jphacks/TK_1621/Fusion360/bin/data/STL_RELEASE/RIGHT_LEG_R.stl

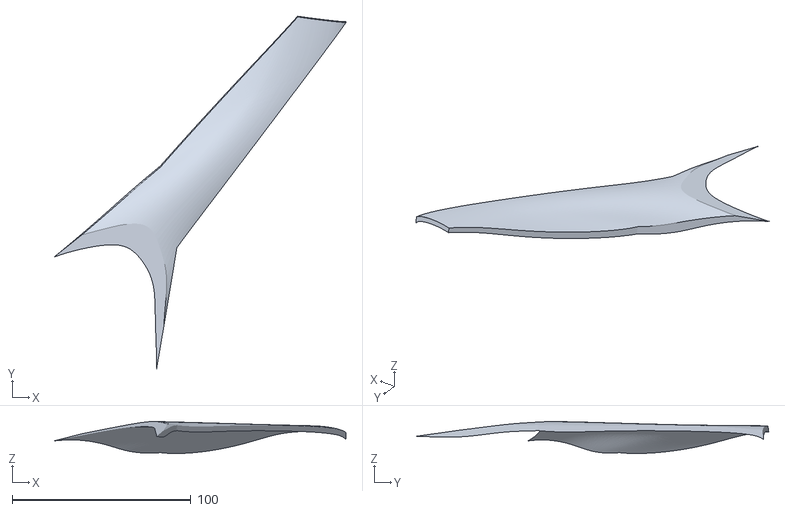
[picture p32: CAD file, 2016-11-25]
Fusion360/bin/data/STL_RELEASE/RIGHT_LEG_R.stl
163.2 x 197.1 x 17.9
