jphacks/TK_1621/Fusion360/bin/data/STL_MATERIAL/MOBILEBATTERY.stl

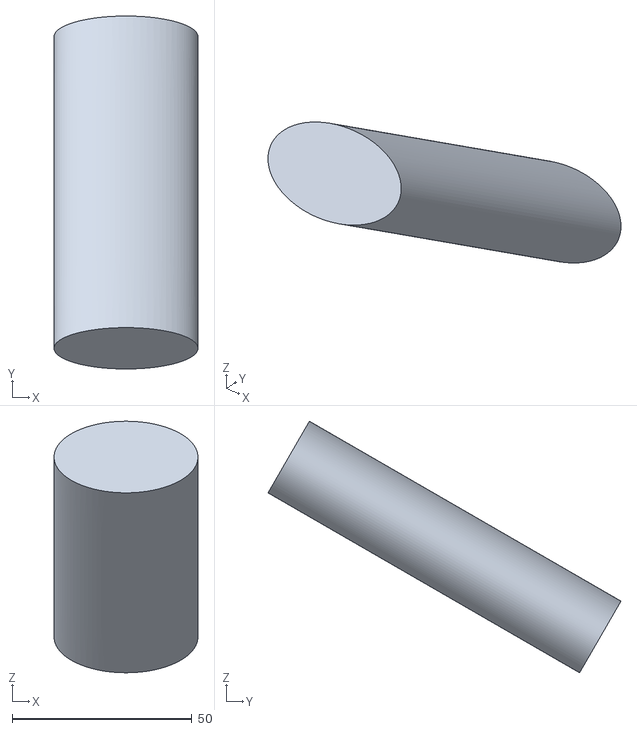
[picture p33: CAD file, 2016-10-29]
Fusion360/bin/data/STL_MATERIAL/MOBILEBATTERY.stl
40.0 x 98.1 x 69.9
