jphacks/TK_1621/Fusion360/bin/data/STL_RELEASE/LEFT_WING_R.stl

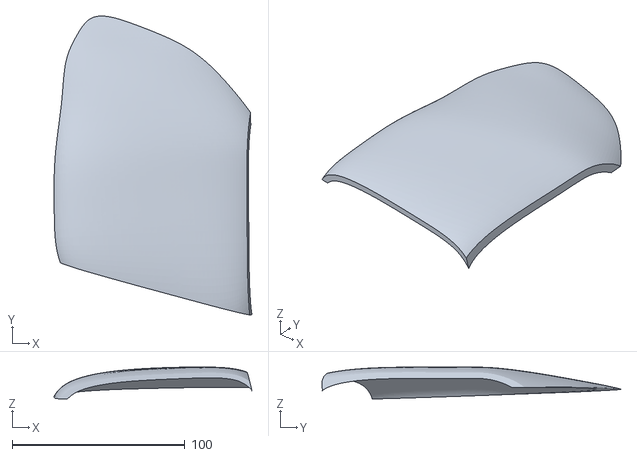
[picture p34: CAD file, 2016-11-25]
Fusion360/bin/data/STL_RELEASE/LEFT_WING_R.stl
114.6 x 173.1 x 18.5
