jphacks/TK_1621/Fusion360/bin/data/OF/RIGHT_LEG.stl

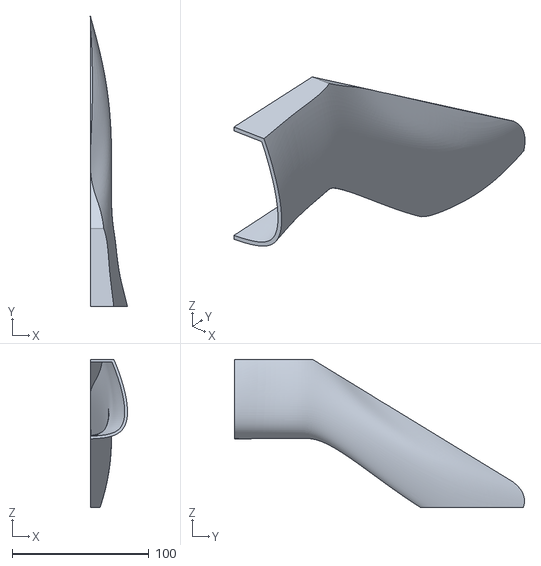
[picture p35: CAD file, 2016-10-30]
Fusion360/bin/data/OF/RIGHT_LEG.stl
27.1 x 211.7 x 108.3
