jphacks/TK_1621/Fusion360/bin/data/STL_RELEASE/BACK_RASP_R.stl

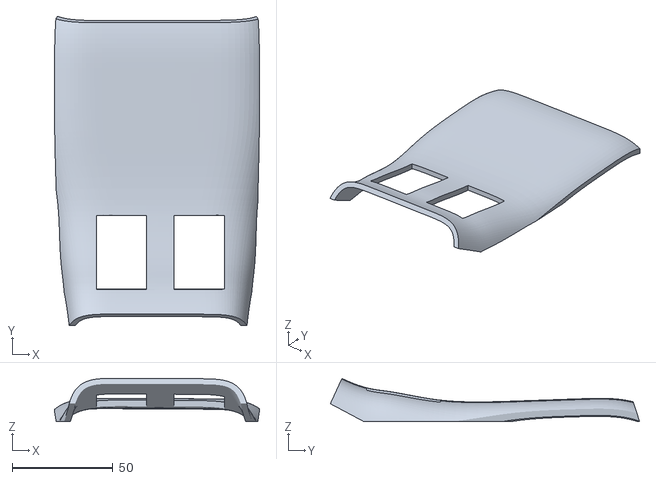
[picture p36: CAD file, 2016-11-25]
Fusion360/bin/data/STL_RELEASE/BACK_RASP_R.stl
101.9 x 153.7 x 21.5
