jphacks/TK_1621/Fusion360/bin/data/STL_RELEASE/FRONT_CAMERA_R.stl

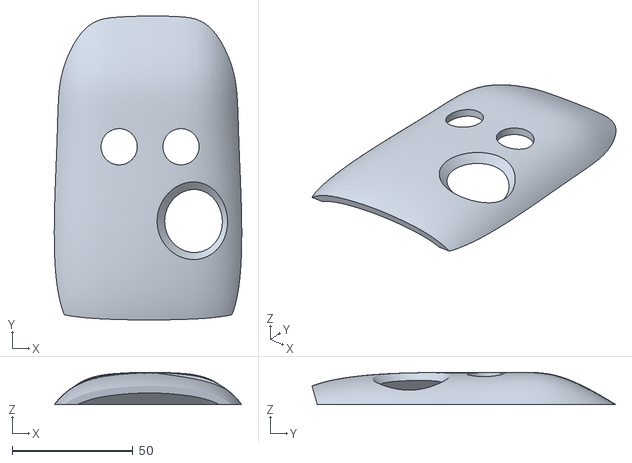
[picture p37: CAD file, 2016-11-25]
Fusion360/bin/data/STL_RELEASE/FRONT_CAMERA_R.stl
77.7 x 125.9 x 13.4
