jphacks/TK_1621/Fusion360/bin/data/STL_MATERIAL/WEBCAM.stl

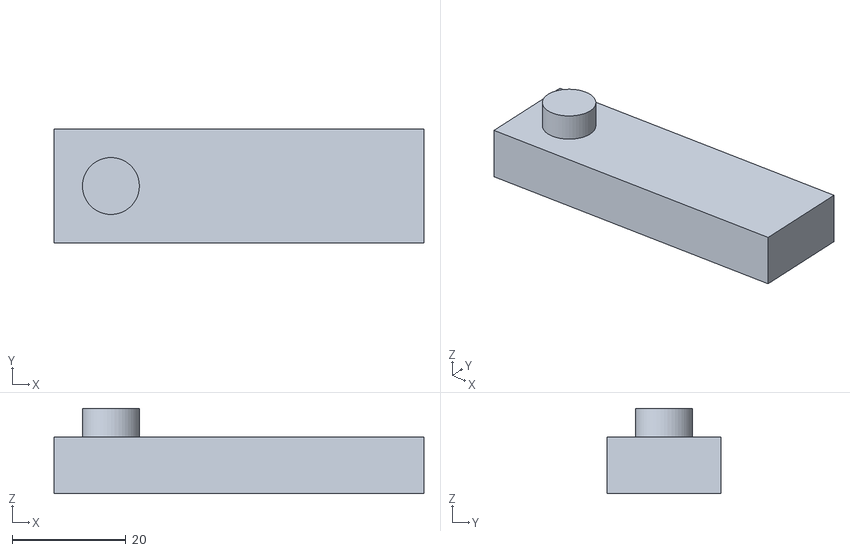
[picture p38: CAD file, 2016-10-29]
Fusion360/bin/data/STL_MATERIAL/WEBCAM.stl
65.0 x 20.0 x 15.0
