jphacks/TK_1621/Fusion360/bin/data/STL_RELEASE/LEFT_LEG_R.stl

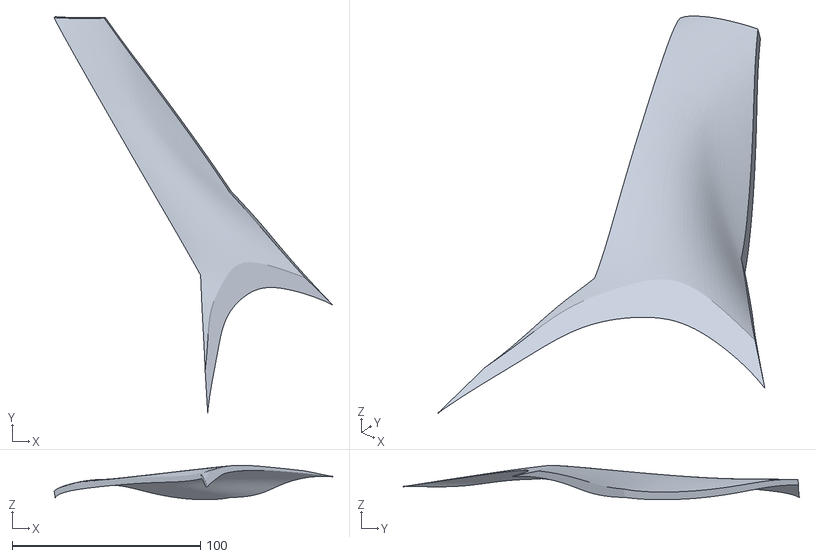
[picture p39: CAD file, 2016-11-25]
Fusion360/bin/data/STL_RELEASE/LEFT_LEG_R.stl
147.9 x 210.1 x 18.3
