jphacks/TK_1621/Fusion360/bin/data/STL_RELEASE/TOP_SPEAKER_R.stl

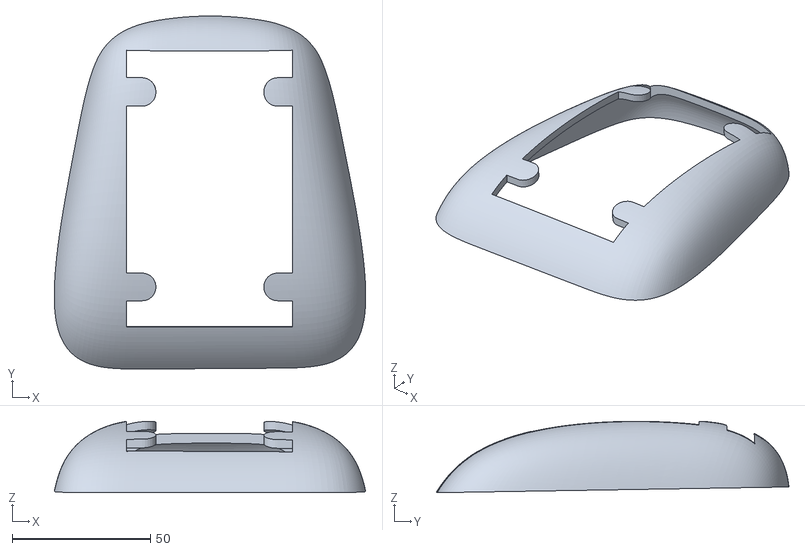
[picture p40: CAD file, 2016-11-25]
Fusion360/bin/data/STL_RELEASE/TOP_SPEAKER_R.stl
112.6 x 127.6 x 25.8
