jphacks/TK_1621/Fusion360/bin/data/STL_MATERIAL/ULTRASONIC.stl

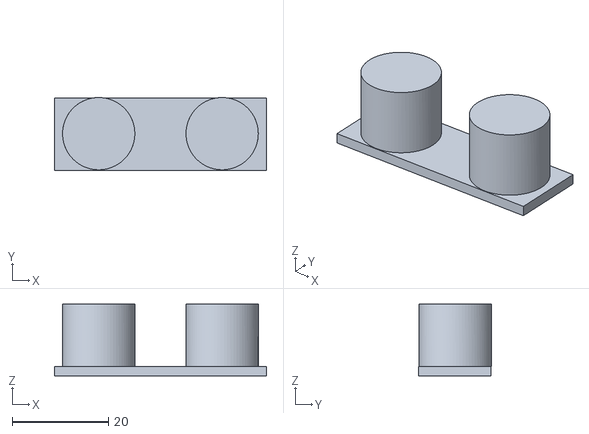
[picture p41: CAD file, 2016-10-29]
Fusion360/bin/data/STL_MATERIAL/ULTRASONIC.stl
44.0 x 15.1 x 14.9
