jphacks/TK_1621/Fusion360/bin/data/STL_MATERIAL/BACK.stl

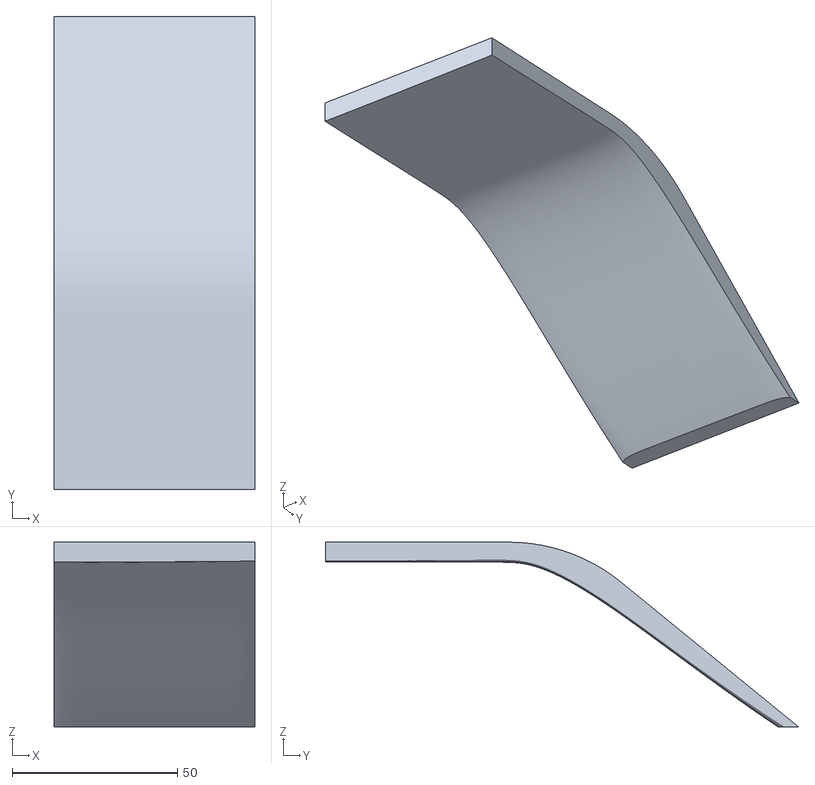
[picture p42: CAD file, 2016-10-29]
Fusion360/bin/data/STL_MATERIAL/BACK.stl
60.8 x 143.2 x 55.9
