jphacks/TK_1621/Fusion360/bin/data/STL_MATERIAL/RASPBERRY.stl

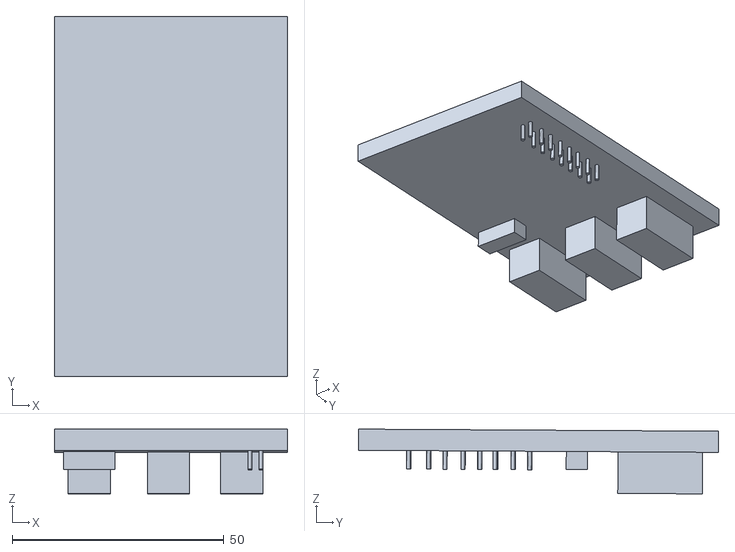
[picture p43: CAD file, 2016-10-29]
Fusion360/bin/data/STL_MATERIAL/RASPBERRY.stl
55.0 x 85.0 x 15.3
