jphacks/TK_1621/Fusion360/bin/data/STL_MATERIAL/PARAMETRICFOUNDATION.stl

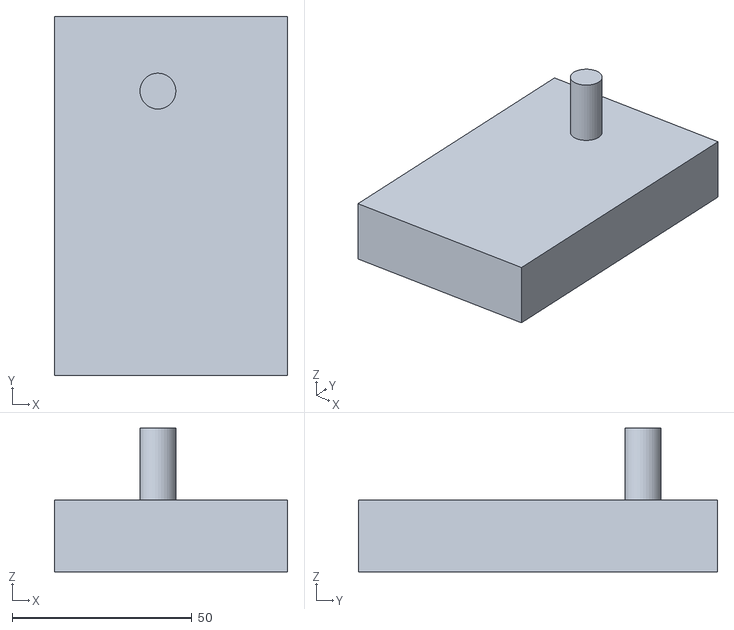
[picture p44: CAD file, 2016-10-29]
Fusion360/bin/data/STL_MATERIAL/PARAMETRICFOUNDATION.stl
65.0 x 100.0 x 40.0
