jphacks/TK_1621/Fusion360/bin/data/STL_MATERIAL/SPEAKER.stl

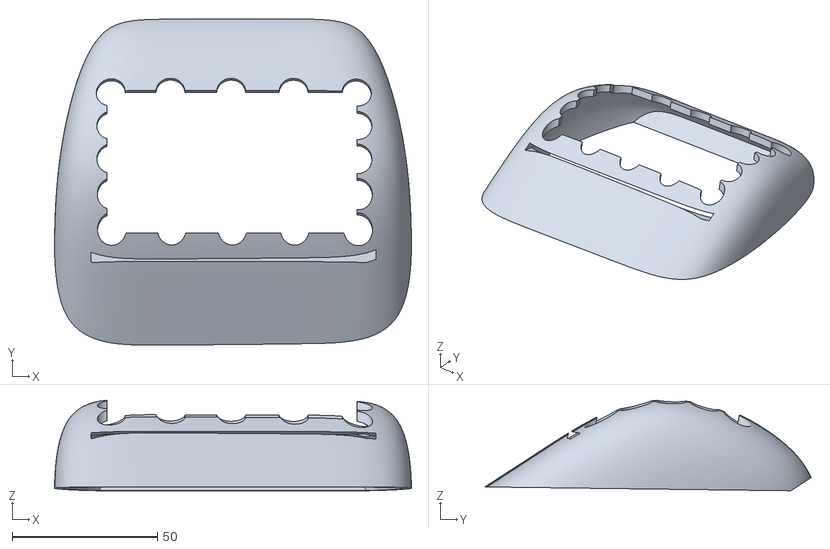
[picture p45: CAD file, 2016-10-29]
Fusion360/bin/data/STL_MATERIAL/SPEAKER.stl
122.8 x 112.3 x 31.2
