jphacks/TK_1621/client/jtalk.py

#!/usr/bin/env python
# -*- coding: utf-8 -*-
#
# created by Keisuke Okumura

# == Kei18 PC ==
# sudo open_jtalk -x /usr/local/Cellar/open-jtalk/1.09/dic
# -m /usr/local/Cellar/open-jtalk/1.09/voice/mei/mei_normal.htsvoice
# -ow out.wav sample.txt
#
# afplay out.wav


import subprocess


def jtalk(t):
    script = './jtalk.sh'
    cmd = ['sh', script, t]
    subprocess.call(cmd)


if __name__ == '__main__':
    text = raw_input("What should I speak? : ") or "こんにちは世界"
    jtalk(text)
